ktanino10/copilot-brick-gift-b/docs/images/B-front-release.png

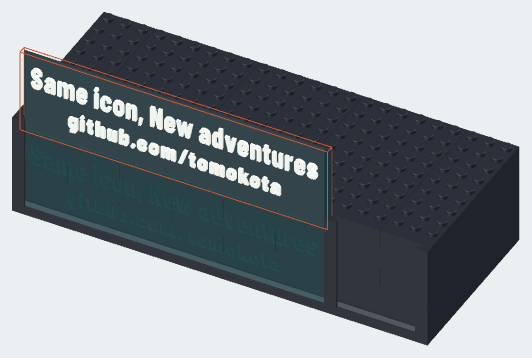
docs/images/B-front-release.png
