ktanino10/copilot-brick-gift-b/docs/images/B-overview-front.png

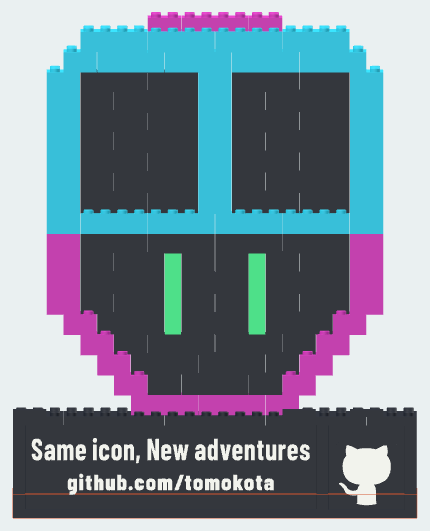
docs/images/B-overview-front.png
