ktanino10/copilot-brick-gift-b/docs/images/B-overview-right.png

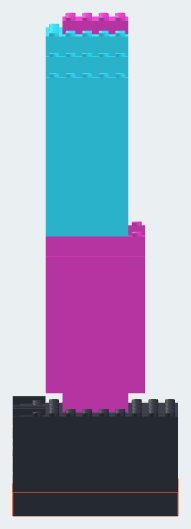
docs/images/B-overview-right.png
