ktanino10/copilot-brick-gift-b/docs/images/B-overview-top.png

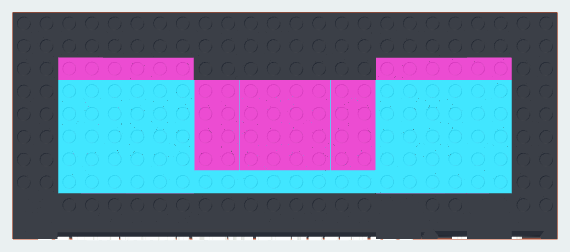
docs/images/B-overview-top.png
