ktanino10/copilot-brick-gift-b/kit/B/plates/B-green-01.3mf

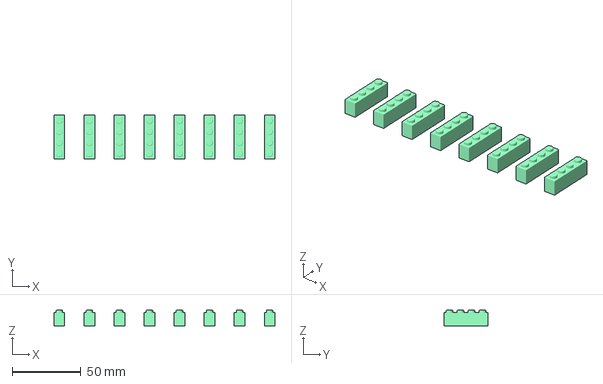
[picture p47: CAD file, 2026-09-19]
kit/B/plates/B-green-01.3mf
160.4 x 31.8 x 11.4 mm
BR-01x04-H096 x 8
