ktanino10/copilot-brick-gift-b/kit/fit/FIT-M-D470.stl

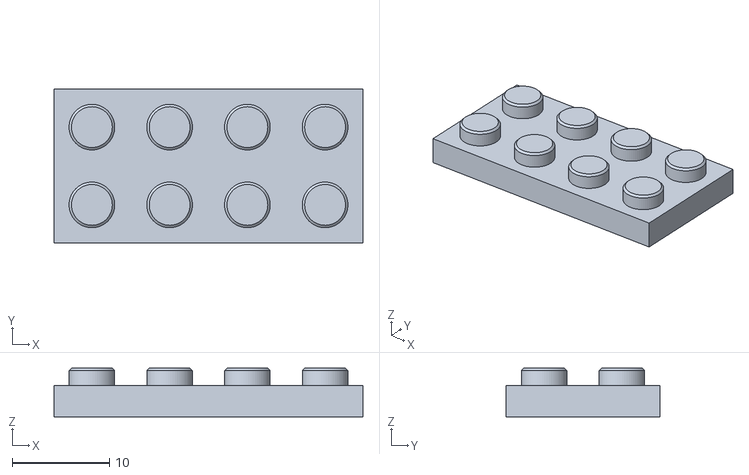
[picture p48: CAD file, 2026-09-19]
kit/fit/FIT-M-D470.stl
31.8 x 15.8 x 5.00
