ktanino10/copilot-brick-gift-b/kit/B/parts/BR-02x04-H064.stl

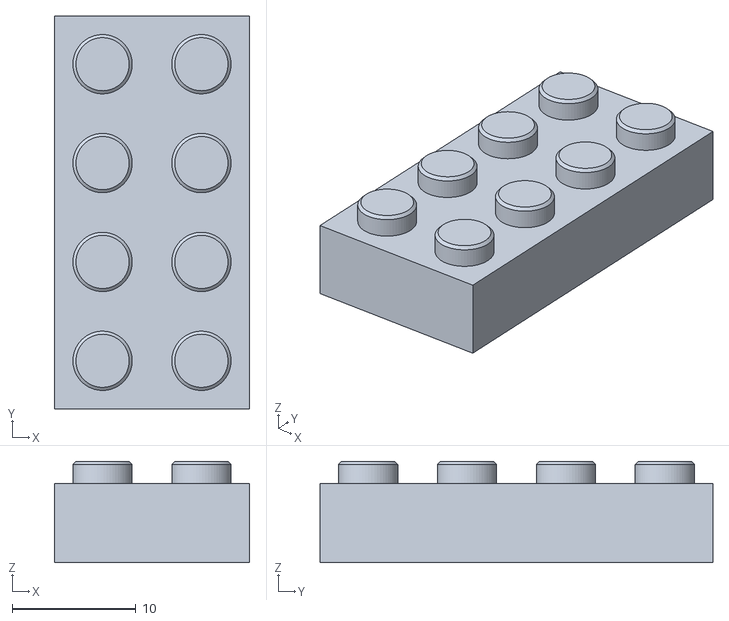
[picture p49: CAD file, 2026-09-19]
kit/B/parts/BR-02x04-H064.stl
15.8 x 31.8 x 8.20
