ktanino10/copilot-brick-gift-b/kit/B/parts/BR-02x05-H096.stl

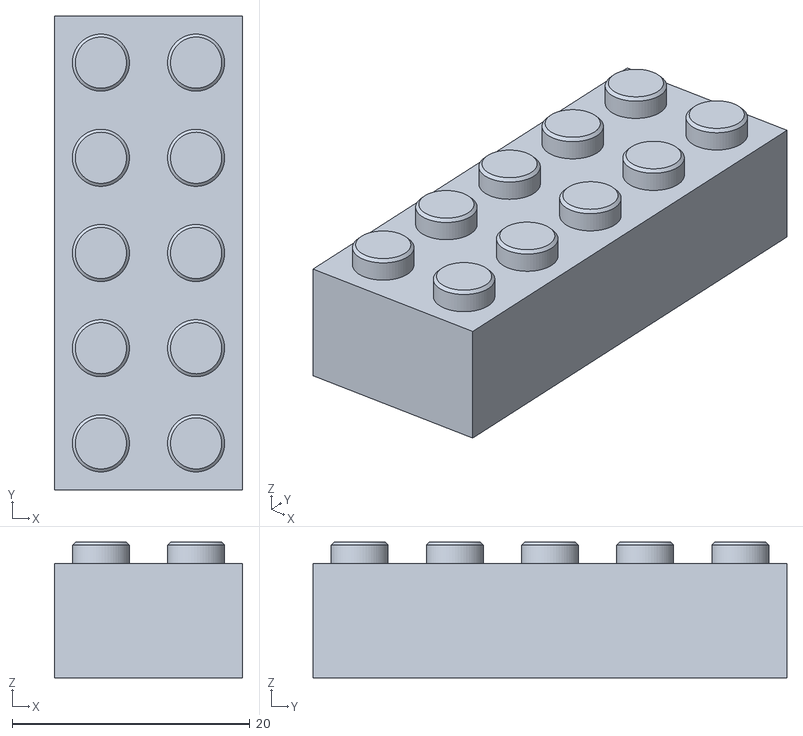
[picture p51: CAD file, 2026-09-19]
kit/B/parts/BR-02x05-H096.stl
15.8 x 39.8 x 11.4
