ktanino10/copilot-brick-gift-b/kit/B/parts/BASE3-03x10-T-d79875.stl

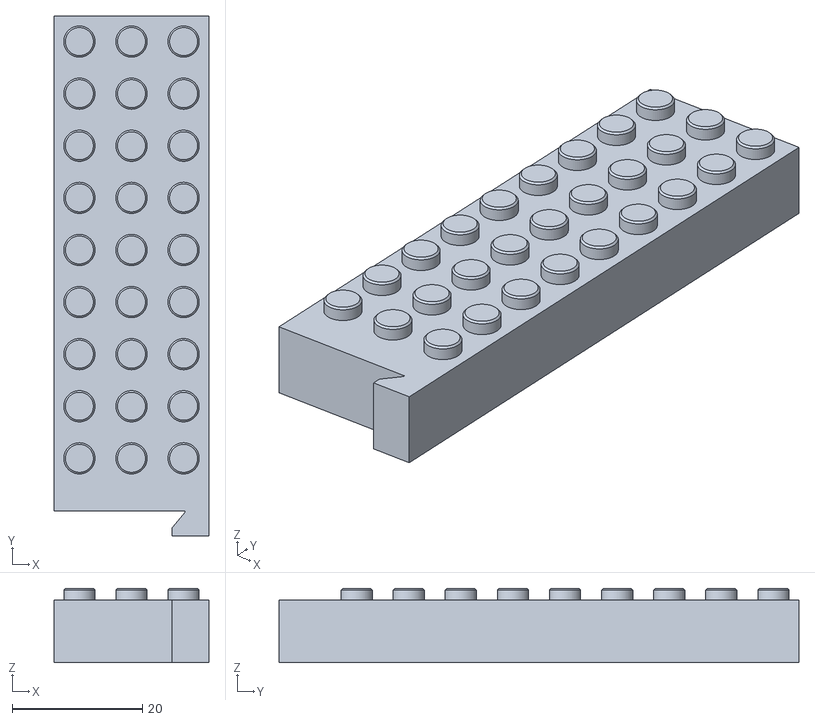
[picture p53: CAD file, 2026-09-19]
kit/B/parts/BASE3-03x10-T-d79875.stl
23.8 x 79.8 x 11.4
