ktanino10/copilot-brick-gift-b/kit/B/plates/B-black-07.3mf

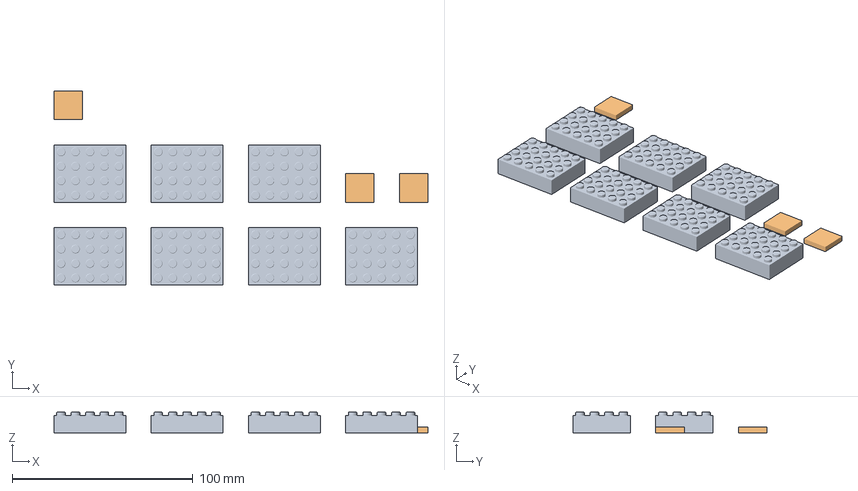
[picture p54: CAD file, 2026-09-19]
kit/B/plates/B-black-07.3mf
207.0 x 107.4 x 11.4 mm
BR-05x04-H096 x 7
NP3-KEEPER x 3
