ktanino10/copilot-brick-gift-b/kit/B/parts/BR-01x04-H096.stl

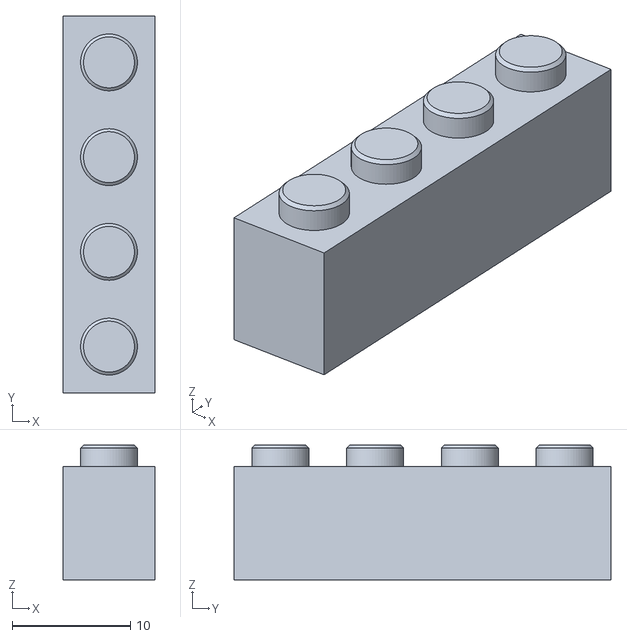
[picture p55: CAD file, 2026-09-19]
kit/B/parts/BR-01x04-H096.stl
7.80 x 31.8 x 11.4
