ktanino10/copilot-brick-gift-b/kit/B/plates/B-cyan-01.3mf

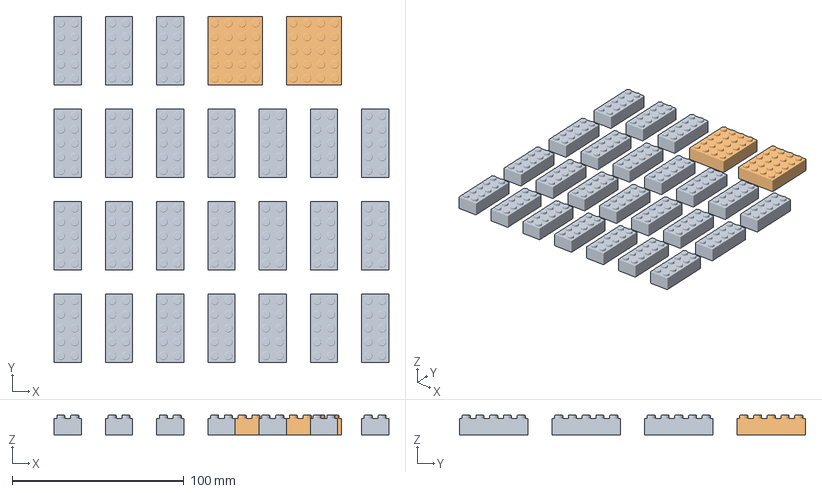
[picture p56: CAD file, 2026-09-19]
kit/B/plates/B-cyan-01.3mf
194.6 x 201.2 x 11.4 mm
BR-02x05-H096 x 24
BR-04x05-H096 x 2
