ktanino10/copilot-brick-gift-b/kit/B/parts/NP3-KEEPER.stl

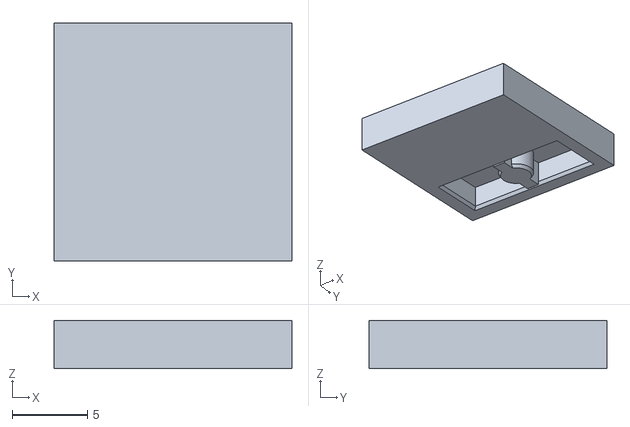
[picture p57: CAD file, 2026-09-19]
kit/B/parts/NP3-KEEPER.stl
15.8 x 15.8 x 3.20
