ktanino10/copilot-brick-gift-b/kit/B/plates/B-black-04.3mf

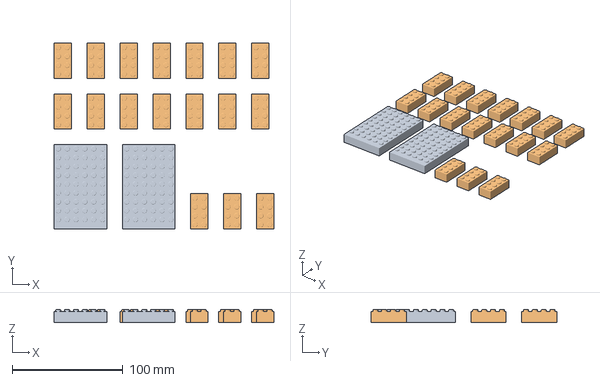
[picture p58: CAD file, 2026-09-19]
kit/B/plates/B-black-04.3mf
199.0 x 168.0 x 11.4 mm
BASE3-06x10-T-838259 x 2
BR-02x04-H096 x 17
