ktanino10/copilot-brick-gift-b/kit/B/plates/B-black-06.3mf

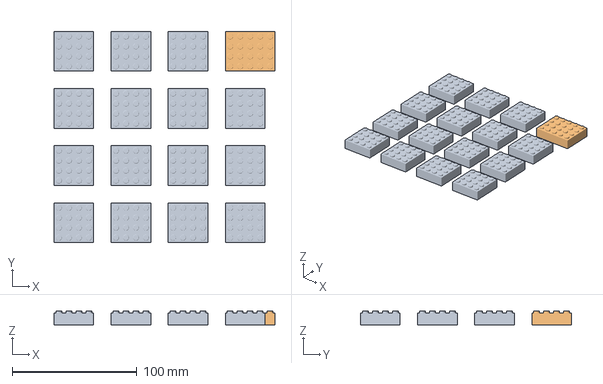
[picture p59: CAD file, 2026-09-19]
kit/B/plates/B-black-06.3mf
177.2 x 169.2 x 11.4 mm
BR-04x04-H096 x 15
BR-05x04-H096
