ktanino10/copilot-brick-gift-b/kit/B/parts/BR-05x04-H096.stl

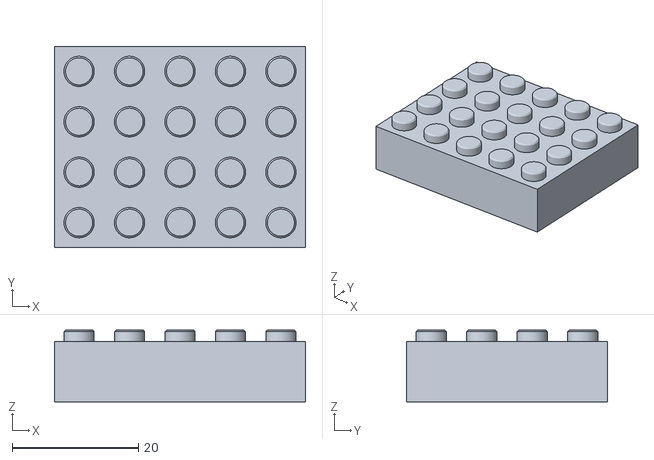
[picture p60: CAD file, 2026-09-19]
kit/B/parts/BR-05x04-H096.stl
39.8 x 31.8 x 11.4
