ktanino10/copilot-brick-gift-b/kit/B/plates/B-black-01.3mf

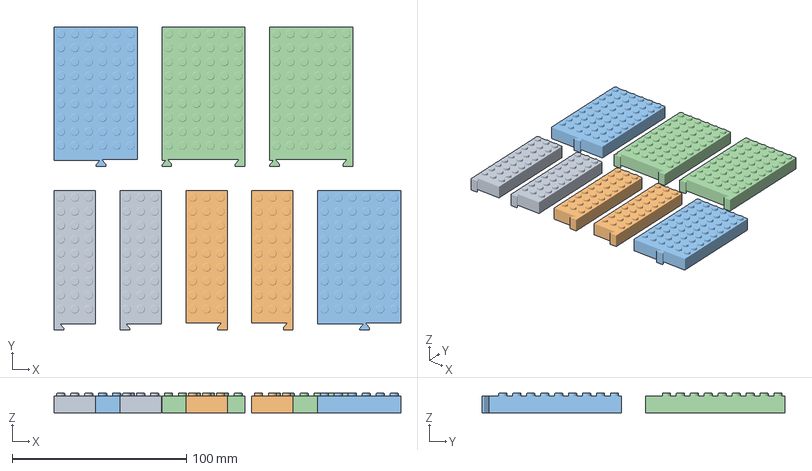
[picture p62: CAD file, 2026-09-19]
kit/B/plates/B-black-01.3mf
199.0 x 173.6 x 11.4 mm
BASE3-03x10-T-aa77a9 x 2
BASE3-03x10-T-d79875 x 2
BASE3-06x10-T-6159e6 x 2
BASE3-06x10-T-6e100f x 2
