ktanino10/copilot-brick-gift-b/kit/B/parts/BR-02x04-H096.stl

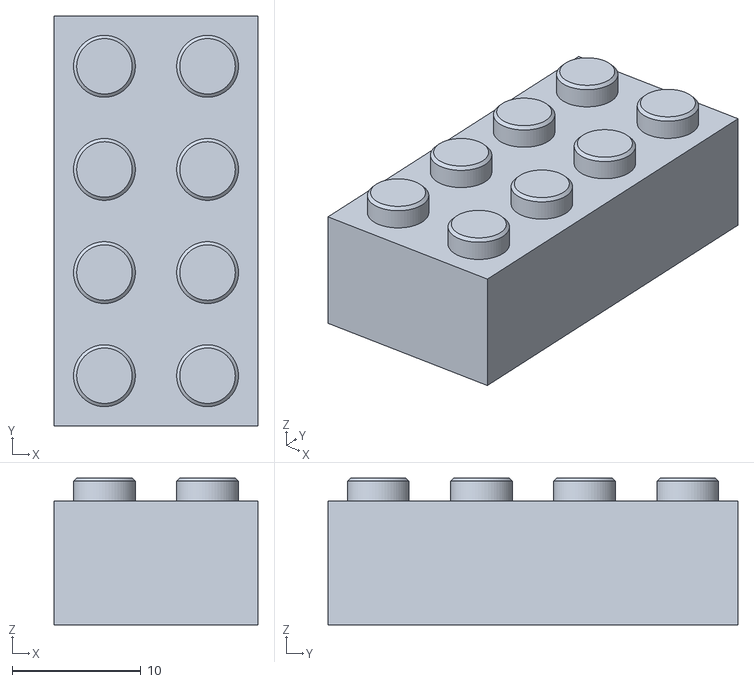
[picture p63: CAD file, 2026-09-19]
kit/B/parts/BR-02x04-H096.stl
15.8 x 31.8 x 11.4
