ktanino10/copilot-brick-gift-b/kit/B/parts/BR-03x04-H096.stl

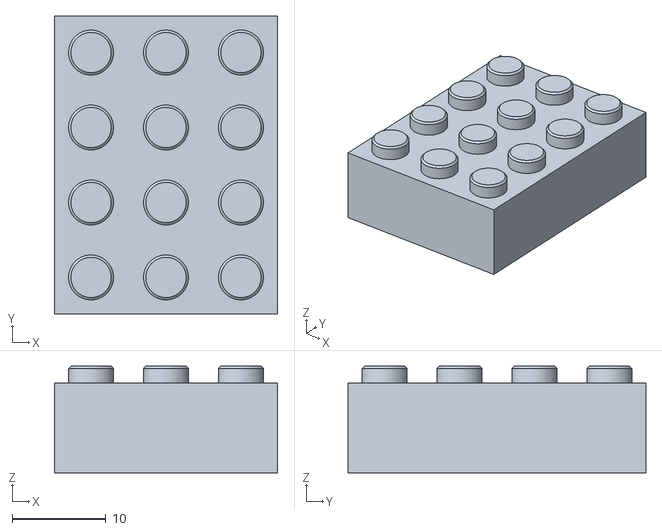
[picture p64: CAD file, 2026-09-19]
kit/B/parts/BR-03x04-H096.stl
23.8 x 31.8 x 11.4
