ktanino10/copilot-brick-gift-b/kit/B/parts/BR-04x04-H064.stl

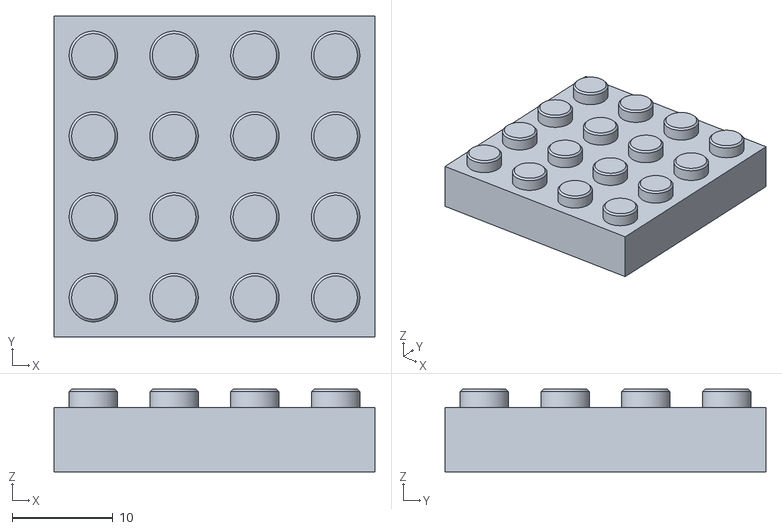
[picture p65: CAD file, 2026-09-19]
kit/B/parts/BR-04x04-H064.stl
31.8 x 31.8 x 8.20
