ktanino10/copilot-brick-gift-b/kit/B/parts/BASE3-24x10-B-562406.stl

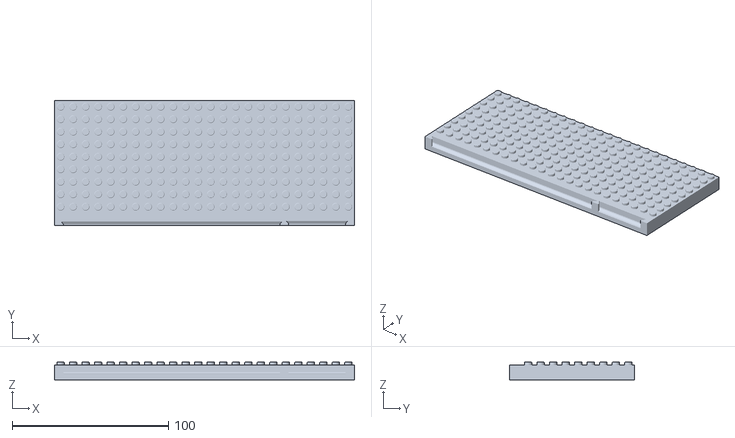
[picture p66: CAD file, 2026-09-19]
kit/B/parts/BASE3-24x10-B-562406.stl
191.8 x 79.8 x 11.4
